SuryaAssistant/prn_s2/OpenHantek6022/docs/images/screenshot_mainwindow.png

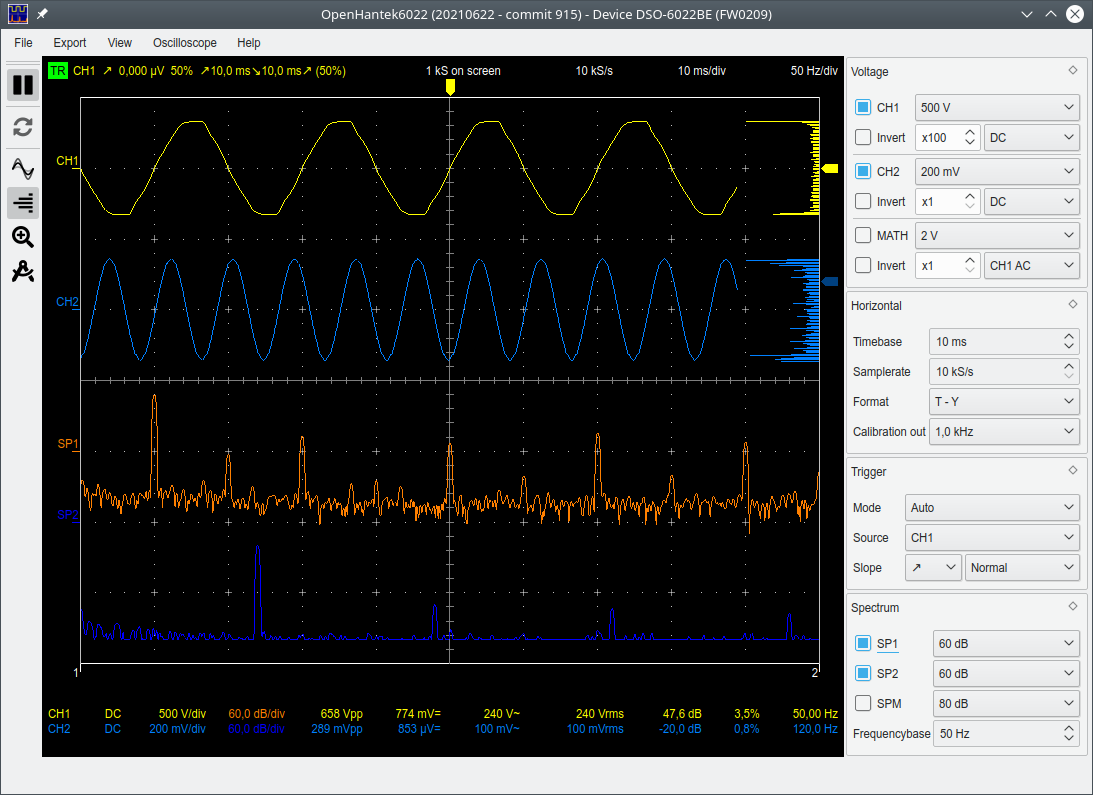
OpenHantek6022/docs/images/screenshot_mainwindow.png
