SuryaAssistant/prn_s2/pcb/prn_s2_bottom.png

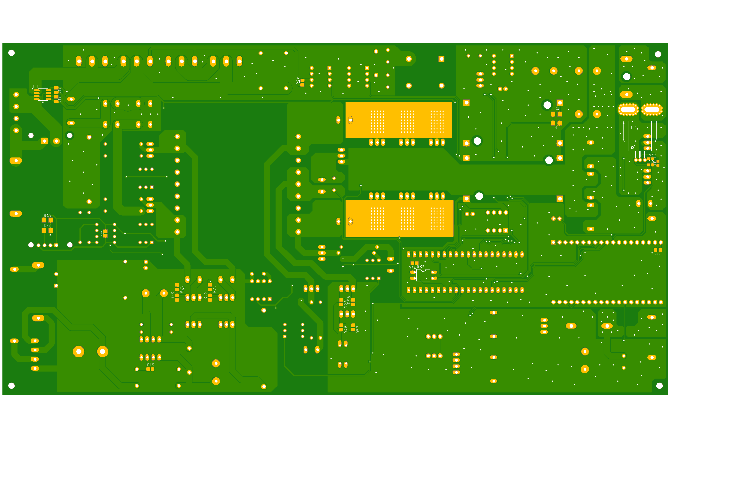
pcb/prn_s2_bottom.png
