SuryaAssistant/prn_s2/pcb/prn_s2_top.png

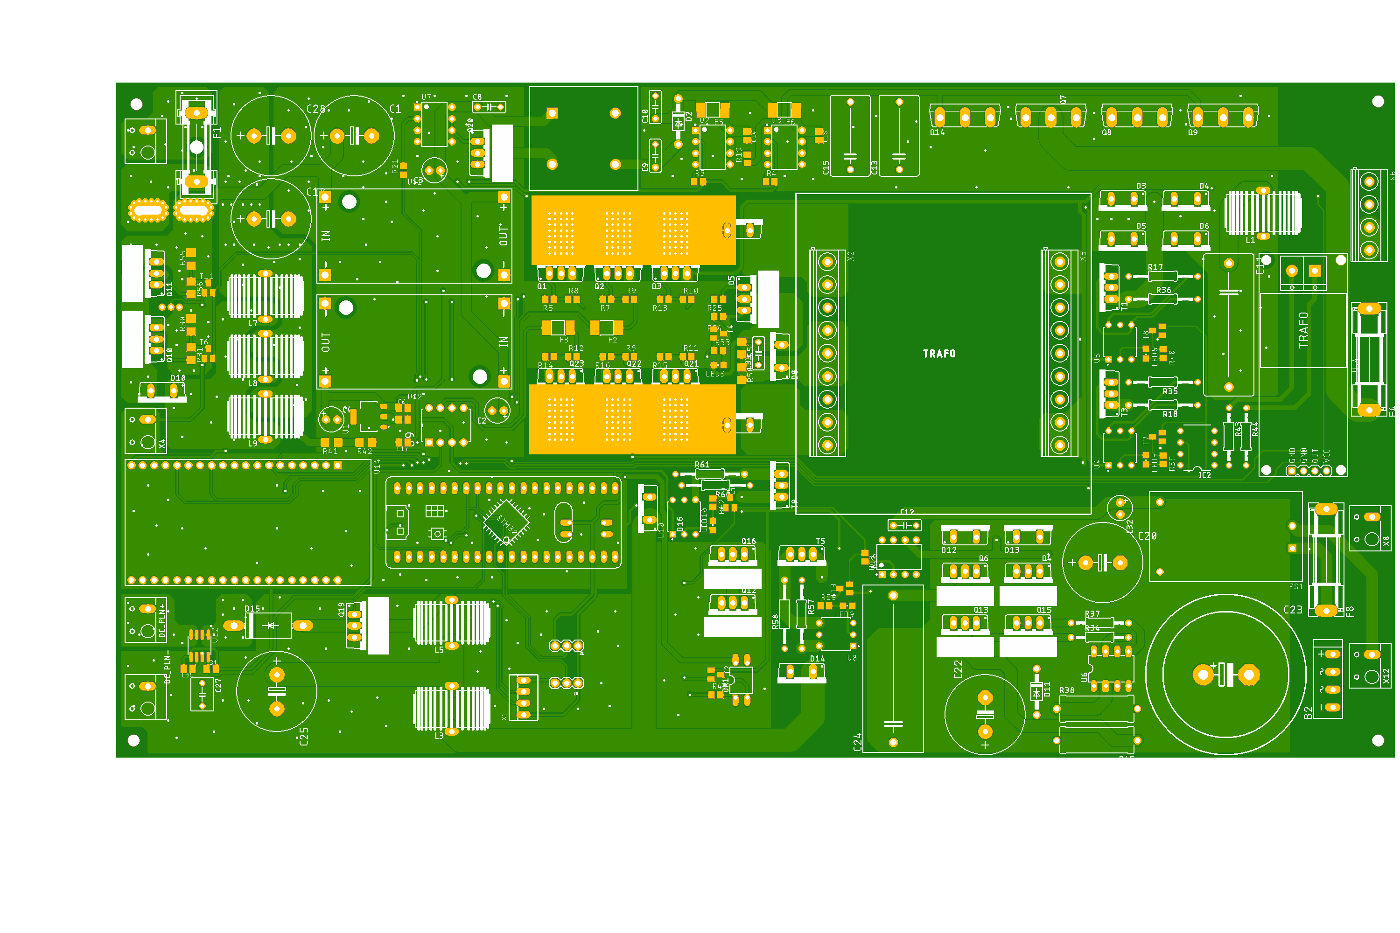
pcb/prn_s2_top.png
